justinbaur/ethanol-module/diagram/ethanolModule.kicad_sch

## KiCad design diagram/ethanolModule.kicad_sch (2026-04-19)

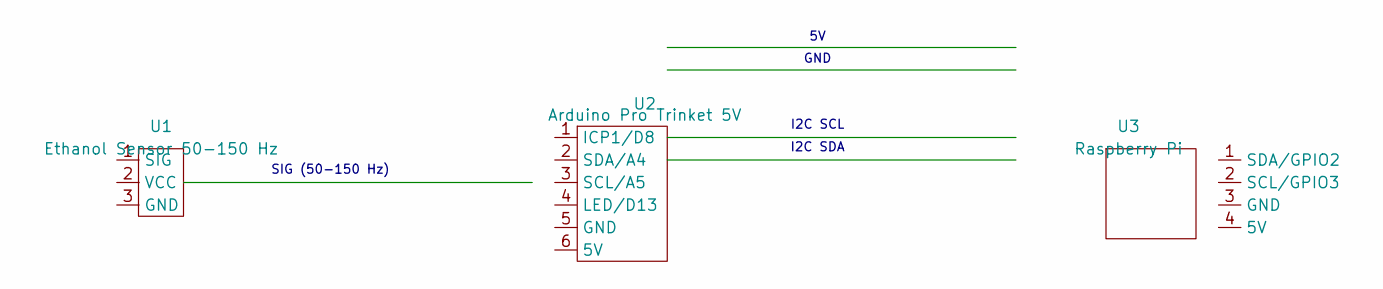
[picture p2: schematic ethanolModule.kicad_sch]

Parts:
U1: Ethanol Sensor 50-150 Hz
U2: Arduino Pro Trinket 5V
U3: Raspberry Pi

Notes on the sheet:
SIG (50-150 Hz)
I2C SDA
I2C SCL
GND
